mzanetti/alfeedo/src/pages/Page.h

/*
This file is part of alfeedo.

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
alfeedo is distributed in the hope that it will be useful, but WITHOUT ANY WARRANTY; 
without even the implied warranty of MERCHANTABILITY or FITNESS FOR A PARTICULAR PURPOSE.
See the GNU General Public License for more details.

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
Copyright (C) 2025-2026 Michael Zanetti <michael_zanetti@gmx.net>
*/

#ifndef PAGE_H
#define PAGE_H

#include <Arduino.h>
#include <Adafruit_SSD1306.h>

#include "DisplayController.h"

#define ICON_WIDTH 16
#define ICON_HEIGHT 16

// https://javl.github.io/image2cpp/

const unsigned char epd_bitmap_wifi[] PROGMEM = {
    0x00, 0x00, 0xe0, 0x07, 0xfc, 0x3f, 0x1e, 0x78, 0xf7, 0xef, 0xff, 0xff, 0xfe, 0x7f, 0xf4, 0x2f,
    0x38, 0x1c, 0xf0, 0x0f, 0xe0, 0x07, 0x80, 0x01, 0xc0, 0x03, 0xc0, 0x03, 0x80, 0x01, 0x00, 0x00};

const unsigned char epd_bitmap_wifi_full[] PROGMEM = {
    0x00, 0x00, 0x00, 0x00, 0xf8, 0x1f, 0xfe, 0x7f, 0xff, 0xff, 0xff, 0xff, 0xfe, 0x7f, 0xfc, 0x3f,
    0xfc, 0x3f, 0xf8, 0x1f, 0xf0, 0x0f, 0xe0, 0x07, 0xc0, 0x03, 0xc0, 0x03, 0x80, 0x01, 0x00, 0x00};

const unsigned char epd_bitmap_clock[] PROGMEM = {
    0xf0, 0x0f, 0x78, 0x1e, 0x9c, 0x39, 0x86, 0x61, 0x87, 0xe1, 0x83, 0xc1, 0x83, 0xc1, 0x81, 0x81,
    0x81, 0x83, 0x03, 0xc7, 0x03, 0xce, 0x07, 0xec, 0x06, 0x60, 0x1c, 0x38, 0x78, 0x1e, 0xf0, 0x0f};

const unsigned char epd_bitmap_alarm[] PROGMEM = {
    0x00, 0x00, 0xfc, 0x3f, 0xfe, 0x7f, 0x9e, 0x79, 0x8e, 0x71, 0x86, 0x61, 0x86, 0x61, 0x86, 0x61,
    0x86, 0x63, 0x06, 0x67, 0x06, 0x6e, 0x0c, 0x34, 0x1c, 0x38, 0xf8, 0x1f, 0xe0, 0x07, 0x00, 0x00};

const unsigned char epd_bitmap_left[] PROGMEM = {
    0x00, 0x60, 0x00, 0x78, 0x00, 0x7e, 0x80, 0x7f, 0xe0, 0x7f, 0xf0, 0x7f, 0xfc, 0x7f, 0xfe, 0x7f,
    0xfe, 0x7f, 0xfc, 0x7f, 0xf0, 0x7f, 0xe0, 0x7f, 0x80, 0x7f, 0x00, 0x7e, 0x00, 0x78, 0x00, 0x60};

const unsigned char epd_bitmap_right[] PROGMEM = {
    0x06, 0x00, 0x1e, 0x00, 0x7e, 0x00, 0xfe, 0x01, 0xfe, 0x07, 0xfe, 0x0f, 0xfe, 0x3f, 0xfe, 0x7f,
    0xfe, 0x7f, 0xfe, 0x3f, 0xfe, 0x0f, 0xfe, 0x07, 0xfe, 0x01, 0x7e, 0x00, 0x1e, 0x00, 0x06, 0x00};

const unsigned char epd_bitmap_empty[] PROGMEM = {
    0xf8, 0x1f, 0xfc, 0x3f, 0x0c, 0x30, 0x0c, 0x30, 0x0c, 0x30, 0x0c, 0x30, 0x0c, 0x30, 0x0c, 0x30,
    0x0c, 0x30, 0x0c, 0x30, 0x0c, 0x30, 0x0c, 0x30, 0x0c, 0x30, 0x0c, 0x30, 0xfc, 0x3f, 0xf8, 0x1f};

// 24x24px
const unsigned char epd_bitmap_warning[] PROGMEM = {
    0x00, 0x00, 0x00, 0x00, 0x3c, 0x00, 0x00, 0x3c, 0x00, 0x00, 0x7e, 0x00, 0x00, 0xe7, 0x00, 0x00,
    0xe7, 0x00, 0x80, 0xc3, 0x01, 0x80, 0x81, 0x01, 0xc0, 0x99, 0x03, 0xc0, 0x18, 0x03, 0xe0, 0x18,
    0x07, 0x70, 0x18, 0x0e, 0x70, 0x18, 0x0e, 0x38, 0x18, 0x1c, 0x18, 0x18, 0x18, 0x1c, 0x00, 0x38,
    0x0c, 0x18, 0x70, 0x0e, 0x18, 0x70, 0x07, 0x18, 0xe0, 0x03, 0x00, 0xc0, 0x03, 0x00, 0xc0, 0xff,
    0xff, 0xff, 0xfe, 0xff, 0x7f, 0x00, 0x00, 0x00};

const unsigned char epd_bitmap_settings[] PROGMEM = {
    0x00, 0x00, 0x00, 0x00, 0x00, 0x00, 0x06, 0x00, 0x00, 0xe0, 0x07, 0x00, 0x00, 0xe1, 0x07, 0x00,
    0x80, 0xfb, 0xdf, 0x01, 0xc0, 0xff, 0xff, 0x03, 0xe0, 0x1f, 0xf8, 0x07, 0xe0, 0x07, 0xe0, 0x07,
    0xc0, 0xf1, 0x8f, 0x03, 0xe0, 0xfc, 0x3f, 0x07, 0xe0, 0x1e, 0x7c, 0x07, 0x7c, 0x0e, 0x70, 0x3e,
    0x7c, 0x07, 0xe0, 0x3e, 0x3c, 0x07, 0xe0, 0x3c, 0x3c, 0x03, 0xc0, 0x3c, 0x3c, 0x03, 0xc0, 0x3c,
    0x3c, 0x03, 0xc0, 0x3c, 0x30, 0x03, 0xc0, 0x0c, 0x30, 0x03, 0xe0, 0x0c, 0x70, 0x07, 0xe0, 0x0e,
    0x7c, 0x0e, 0x70, 0x3e, 0xfc, 0x3e, 0x78, 0x1f, 0xf8, 0xfc, 0x3f, 0x1f, 0xf0, 0xf1, 0x8f, 0x0f,
    0xf0, 0x07, 0xe0, 0x0f, 0x00, 0x1f, 0xf8, 0x00, 0x00, 0xfe, 0x7f, 0x00, 0x00, 0xfe, 0x7f, 0x00,
    0x00, 0x7e, 0x7e, 0x00, 0x00, 0x38, 0x1c, 0x00, 0x00, 0x00, 0x00, 0x00, 0x00, 0x00, 0x00, 0x00};

class Engine;
class FillSensor;
class OTAManager;

class Page
{
public:
    Page(const String &name);
    ~Page() = default;
    String name() const;
    virtual void render(Adafruit_SSD1306 &display, Engine *engine, FillSensor *FillSensor, OTAManager *otaManager) = 0;
    virtual void handleInput(DisplayController *controller, Engine *engine, DisplayController::ButtonInput input);
    virtual void reset() {};
    virtual bool autoExit() const { return true; };

protected:
    void drawTitle(Adafruit_GFX &display, const String &text, const unsigned char* iconData);
    void drawMenu(Adafruit_GFX & display, int cycle, int selection, const String &line1Text, int line1Size, const String &line2Text = String(), int line2Size = 1);

    void drawCenteredText(Adafruit_GFX & display, int cycle, const String &line1Text, int line1Size, const String &line2Text = String(), int line2Size = 1);
    void drawScrollingLabel(Adafruit_GFX &display, int cycle, const String &text, bool selected, int yOffset);
    void drawBarControl(Adafruit_GFX &display, float value, float minValue, float maxValue, int yOffset);
    
    void exit(DisplayController * controller);
    bool needsTimedRefresh() const;

private:
    String m_name;
    mutable uint16_t m_lastRefresh = 0;
};
#endif // PAGE_H
